longvubach/Graduation-Project/Assets/IMG_1062.JPG

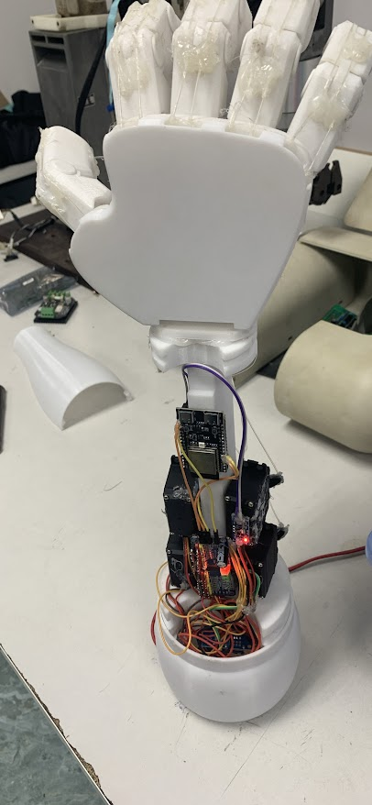
Assets/IMG_1062.JPG
