longvubach/Graduation-Project/Assets/IMG_1064.JPG

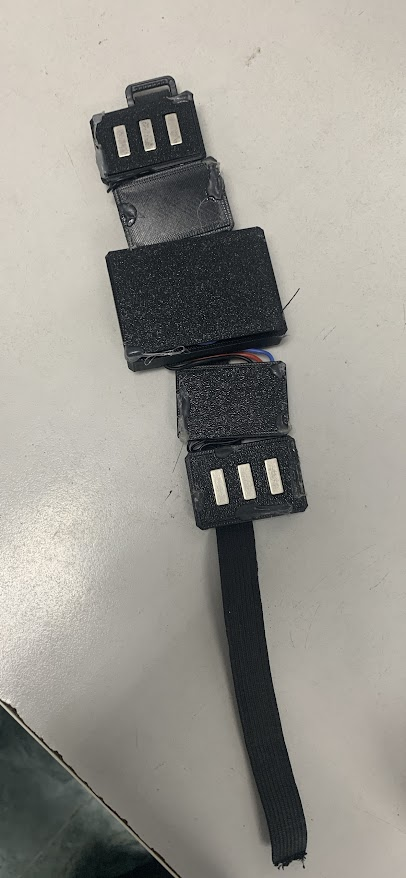
Assets/IMG_1064.JPG
