longvubach/Graduation-Project/Assets/IMG_1065.JPG

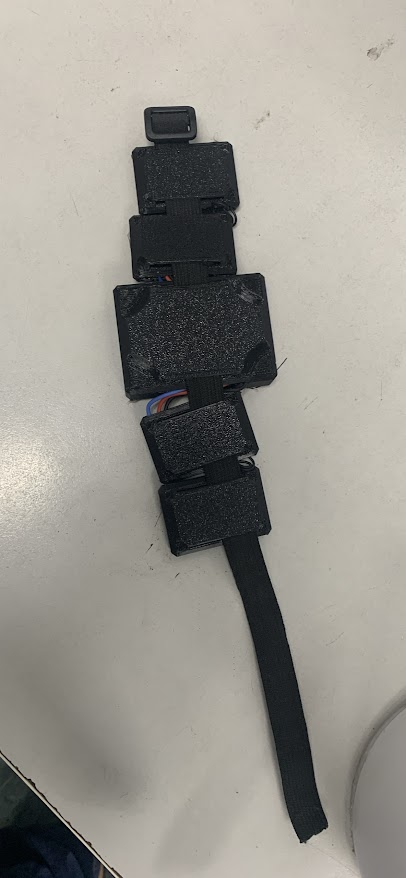
Assets/IMG_1065.JPG
