longvubach/Graduation-Project/Assets/IMG_1084.jpg

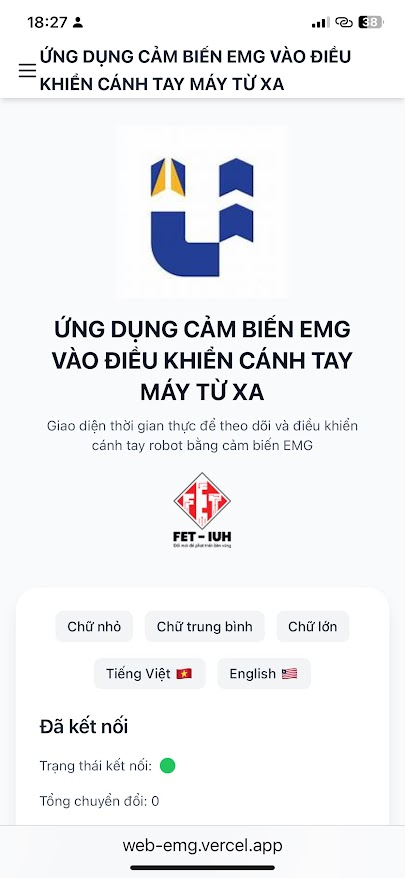
Assets/IMG_1084.jpg
