longvubach/Graduation-Project/Assets/IMG_1085.jpg

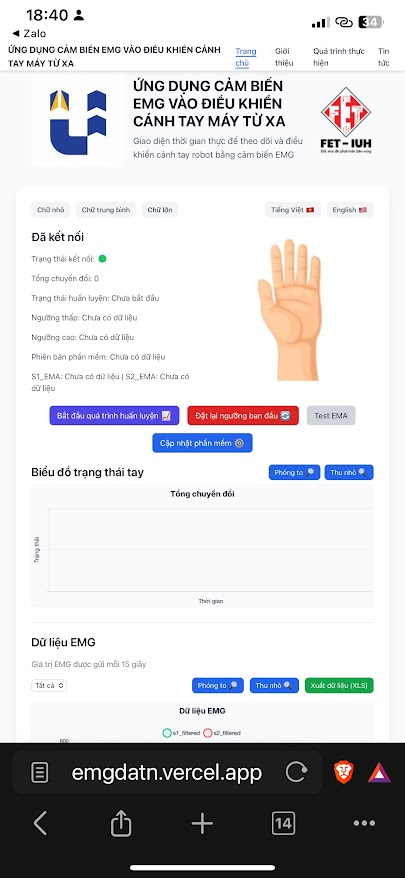
Assets/IMG_1085.jpg
