longvubach/Graduation-Project/Assets/IMG_1086.jpg

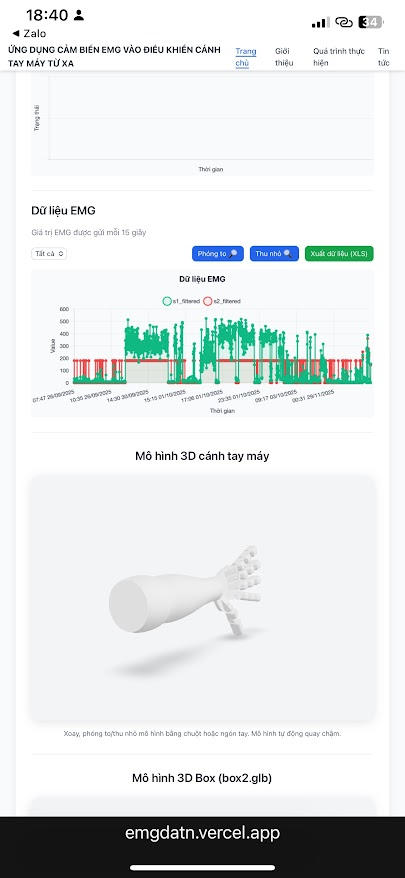
Assets/IMG_1086.jpg
