longvubach/Graduation-Project/Assets/IMG_1087.jpg

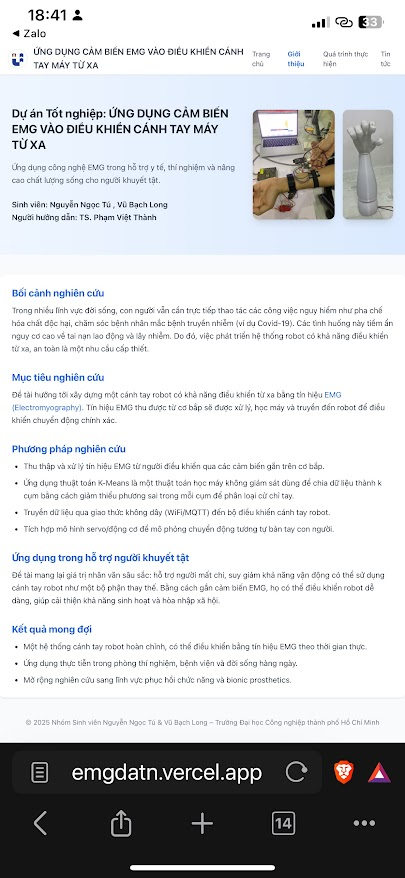
Assets/IMG_1087.jpg
