longvubach/Graduation-Project/Assets/IMG_1088.jpg

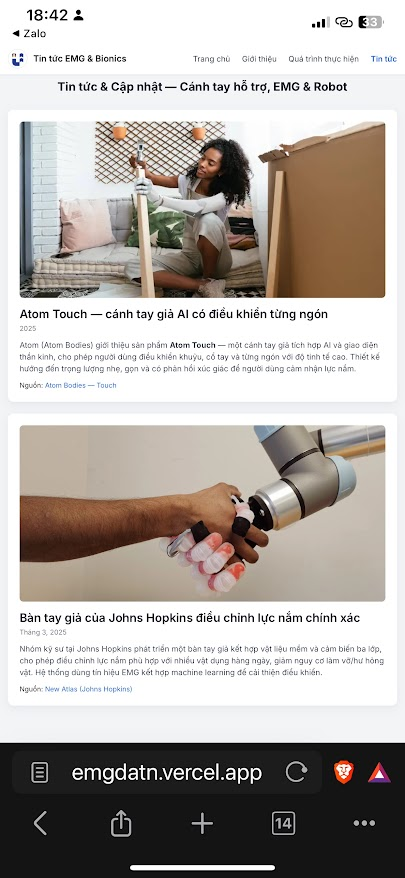
Assets/IMG_1088.jpg
