longvubach/Graduation-Project/Assets/IMG_1089.jpg

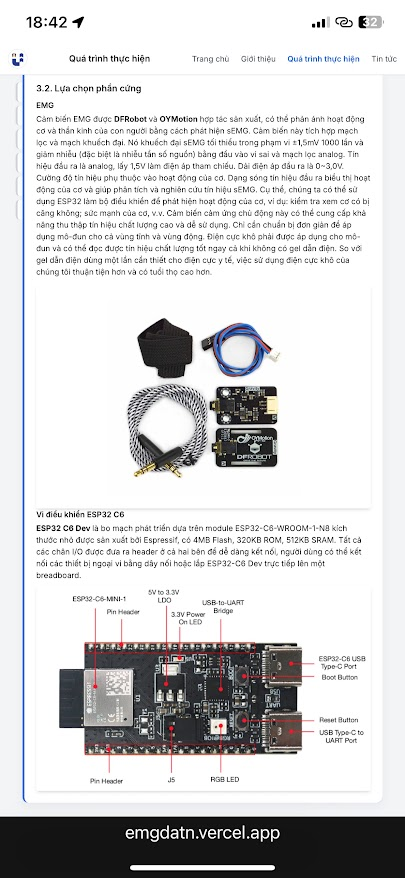
Assets/IMG_1089.jpg
