longvubach/Graduation-Project/Assets/IMG_1091.jpg

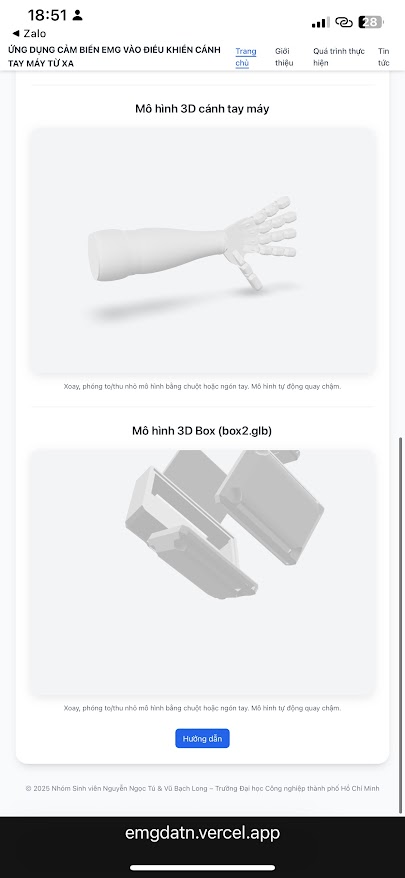
Assets/IMG_1091.jpg
