longvubach/Graduation-Project/Assets/IMG_1112.JPG

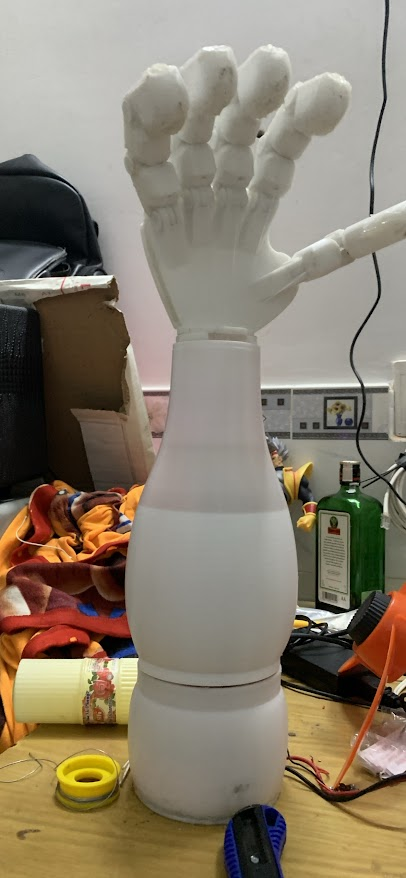
Assets/IMG_1112.JPG
